robotfishe/thresher-shark-horizon/left-half/lasercut-files/left-base.dxf

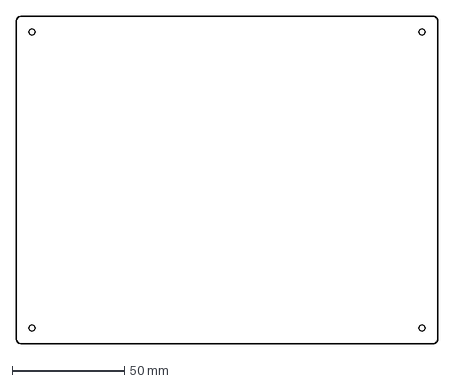
[picture p17: CAD file, 2025-04-30]
left-half/lasercut-files/left-base.dxf
188.0 x 146.0 mm
