robotfishe/thresher-shark-horizon/right-half/lasercut-files/right-plate-support.dxf

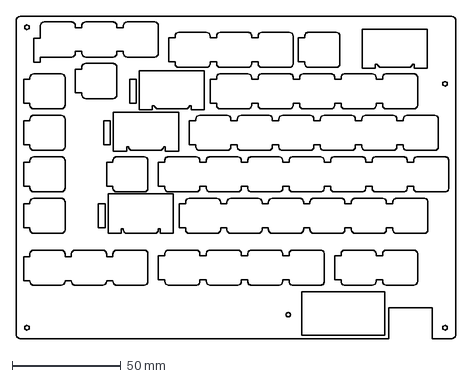
[picture p18: CAD file, 2025-04-30]
right-half/lasercut-files/right-plate-support.dxf
202.0 x 148.0 mm
