robotfishe/thresher-shark-horizon/left-half/lasercut-files/left-connector-cover.dxf

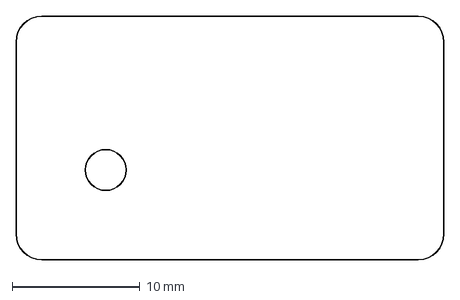
[picture p19: CAD file, 2025-04-30]
left-half/lasercut-files/left-connector-cover.dxf
33.4 x 19.0 mm
