robotfishe/thresher-shark-horizon/left-half/lasercut-files/left-pcb-support.dxf

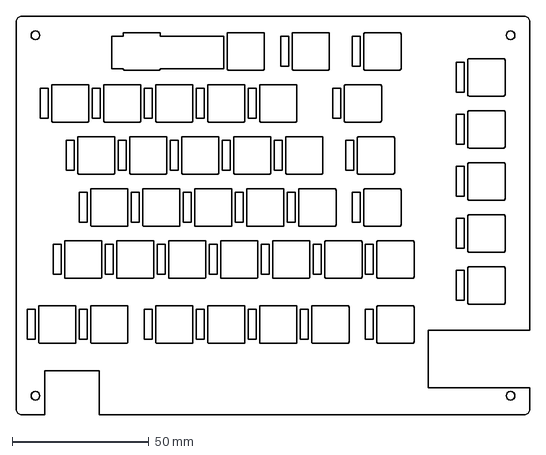
[picture p20: CAD file, 2025-04-30]
left-half/lasercut-files/left-pcb-support.dxf
188.0 x 146.0 mm
