robotfishe/thresher-shark-horizon/left-half/lasercut-files/left-mcu-spacer.dxf

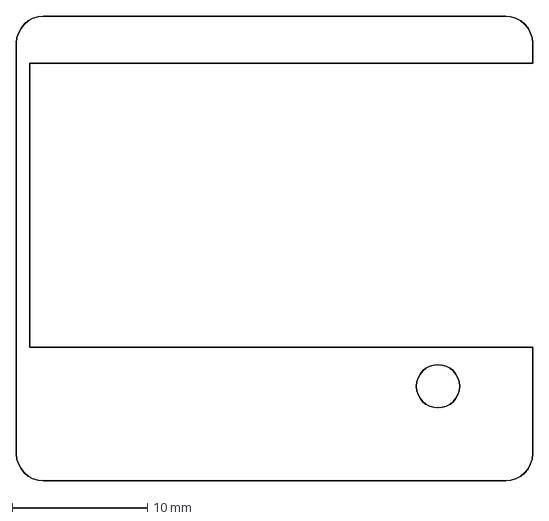
[picture p21: CAD file, 2025-04-30]
left-half/lasercut-files/left-mcu-spacer.dxf
38.2 x 34.4 mm
